dongseon-jeong/leg_demo/train_arm/humanoid_urdf_description/meshes/rgrip_gear_1.stl

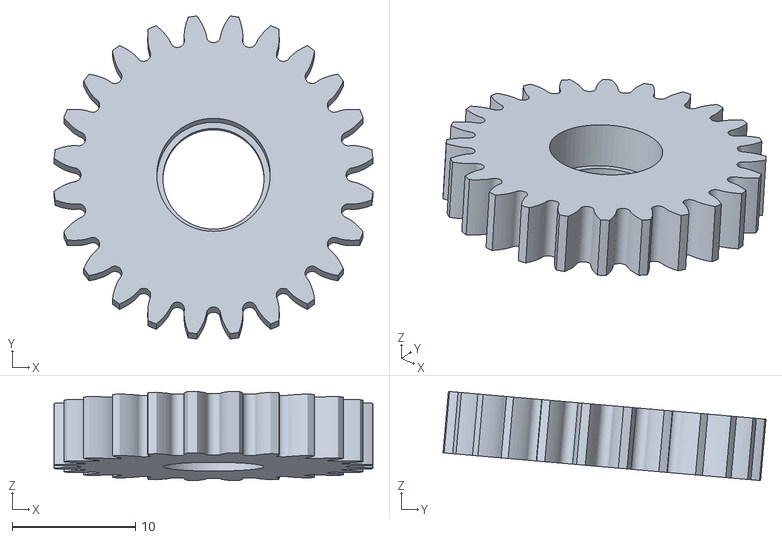
[picture p29: CAD file, 2026-08-16]
train_arm/humanoid_urdf_description/meshes/rgrip_gear_1.stl
25.9 x 26.2 x 7.23
