dongseon-jeong/leg_demo/3d/rl2.stl

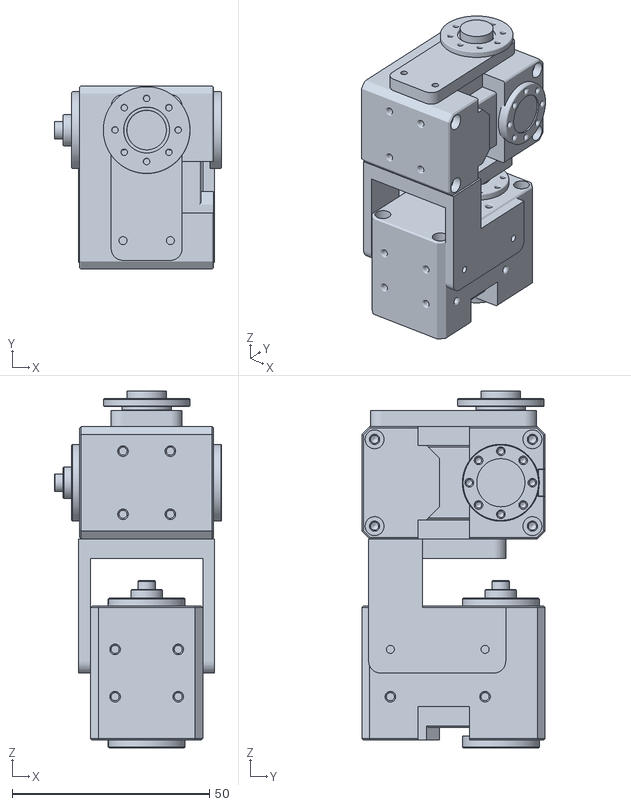
[picture p30: CAD file, 2025-12-05]
3d/rl2.stl
42.4 x 46.5 x 90.5
