dongseon-jeong/leg_demo/legs_description/meshes/rl3_1.stl

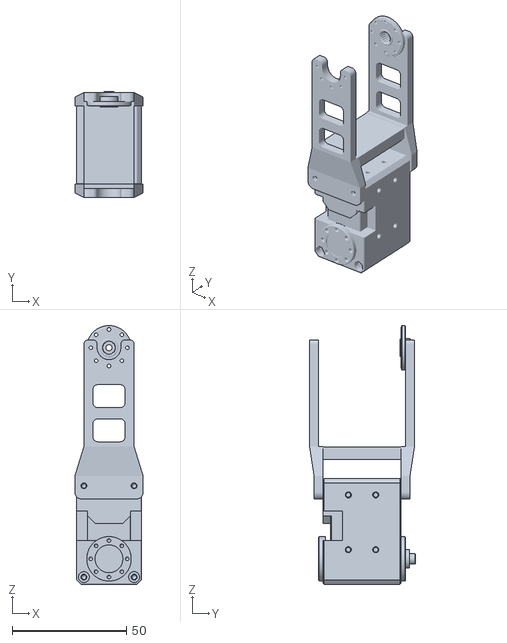
[picture p31: CAD file, 2025-12-05]
legs_description/meshes/rl3_1.stl
30.0 x 46.4 x 113.5
