dongseon-jeong/leg_demo/train_arm/humanoid_urdf_description/meshes/rgrip_fin1_1.stl

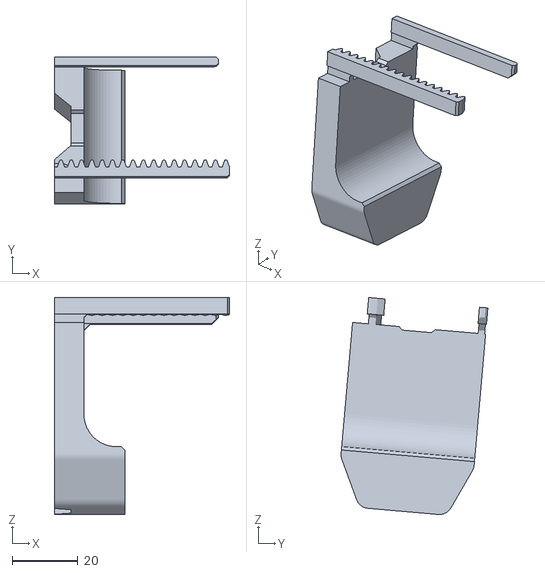
[picture p32: CAD file, 2026-08-16]
train_arm/humanoid_urdf_description/meshes/rgrip_fin1_1.stl
53.4 x 44.7 x 66.1
