dongseon-jeong/leg_demo/3d/rl3.stl

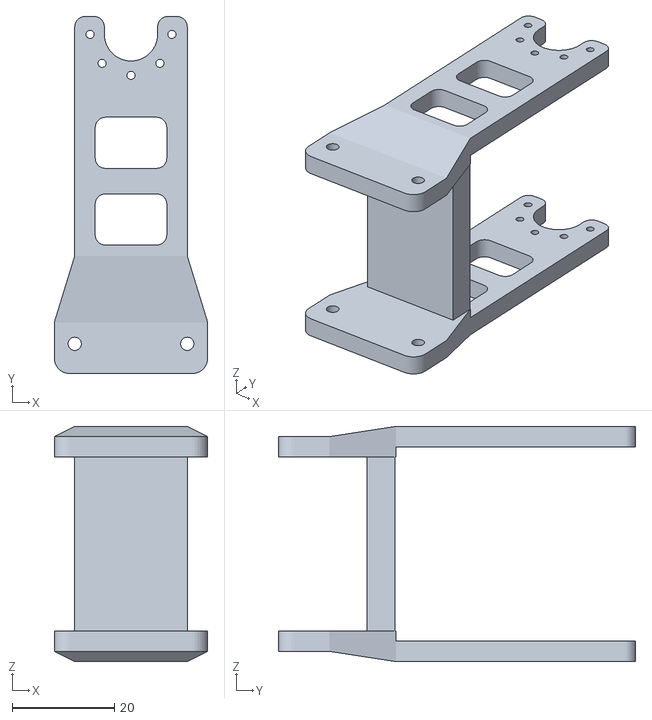
[picture p33: CAD file, 2025-12-05]
3d/rl3.stl
30.0 x 69.8 x 46.0
