dongseon-jeong/leg_demo/legs_description/meshes/base_link.stl

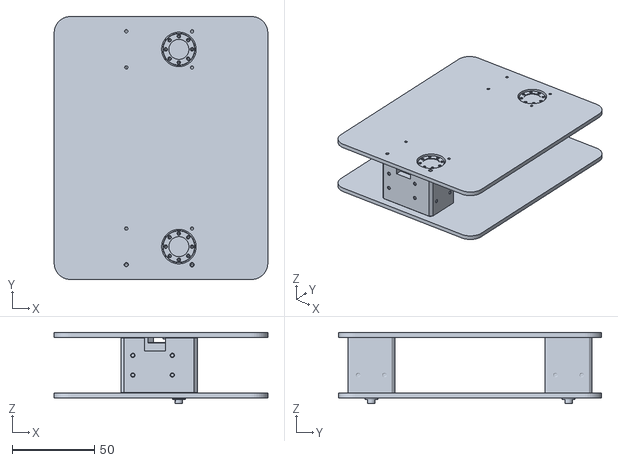
[picture p34: CAD file, 2025-12-05]
legs_description/meshes/base_link.stl
130.0 x 160.0 x 43.4
