dongseon-jeong/leg_demo/train_arm/humanoid_urdf_description/meshes/relbow_1.stl

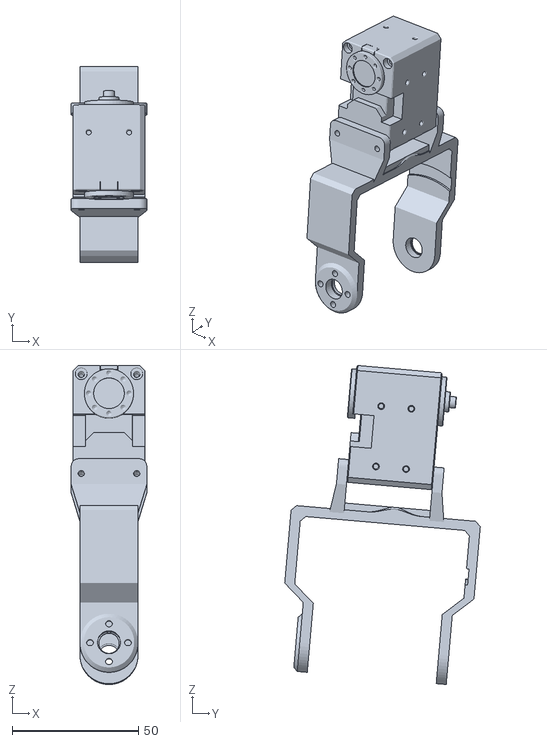
[picture p35: CAD file, 2026-08-16]
train_arm/humanoid_urdf_description/meshes/relbow_1.stl
30.0 x 77.5 x 126.5
