dongseon-jeong/leg_demo/train_arm/humanoid_urdf_description/meshes/lwrist_1.stl

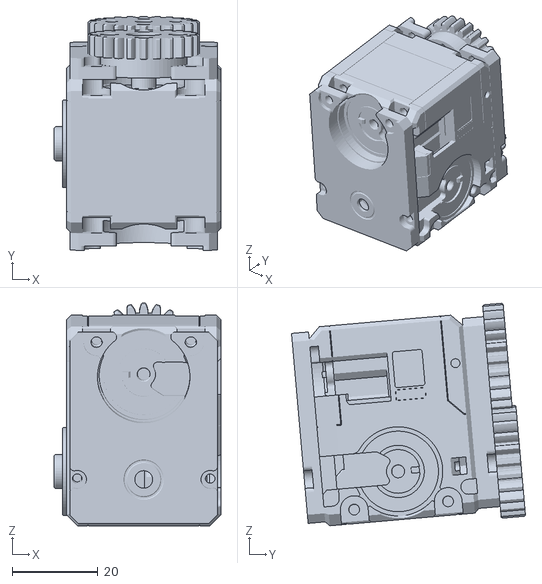
[picture p36: CAD file, 2026-08-16]
train_arm/humanoid_urdf_description/meshes/lwrist_1.stl
38.9 x 54.6 x 51.9
